paulpf/water-tank-monitor/docs/hardware/20260521_123843.jpg

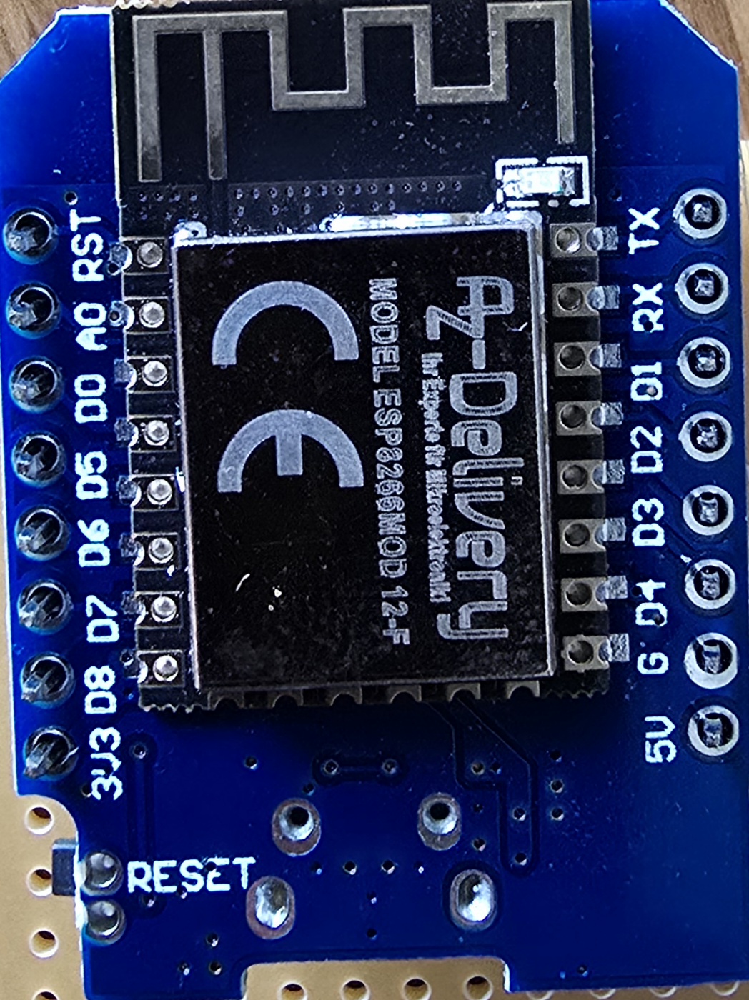
docs/hardware/20260521_123843.jpg
