paulpf/water-tank-monitor/docs/hardware/20260521_123853.jpg

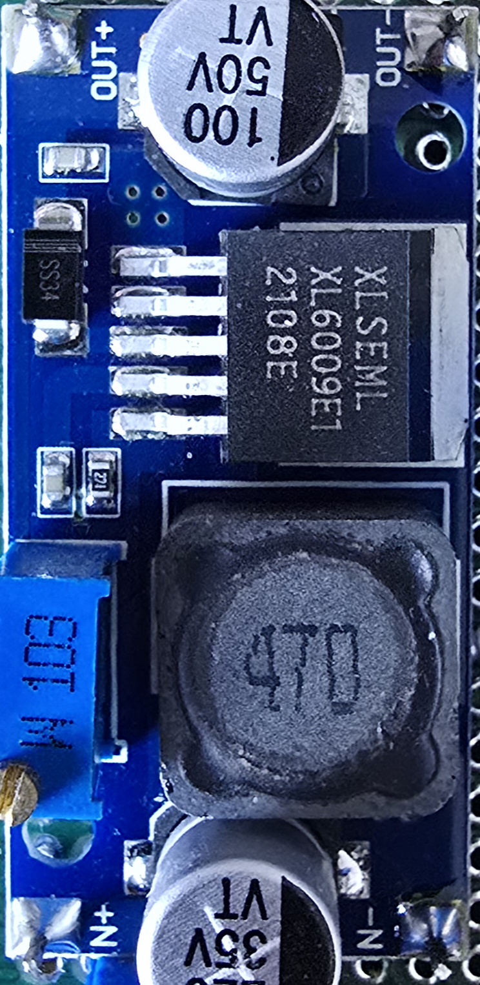
docs/hardware/20260521_123853.jpg
