paulpf/water-tank-monitor/docs/hardware/20260521_123857.jpg

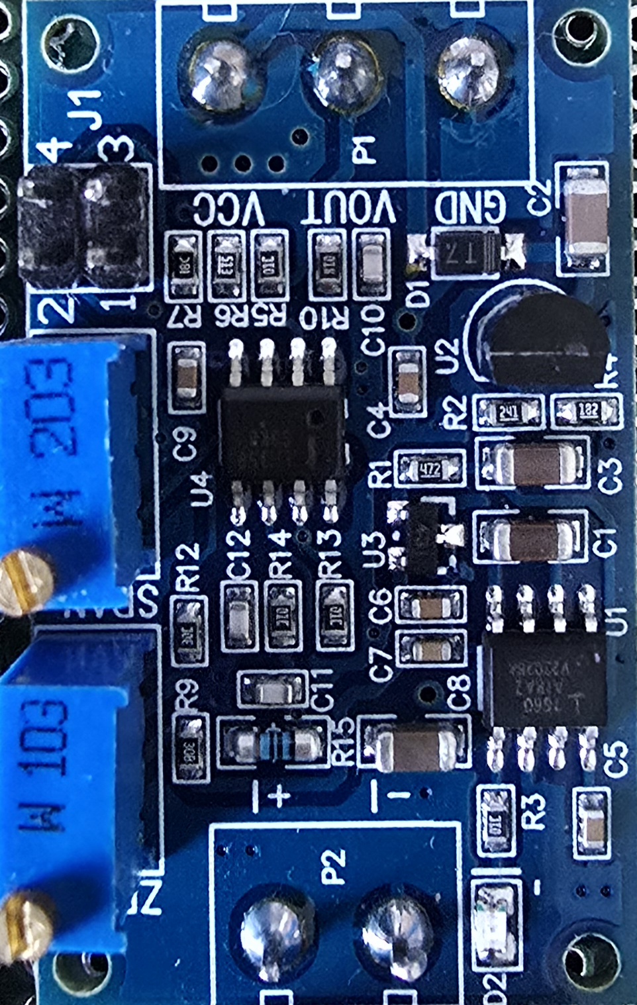
docs/hardware/20260521_123857.jpg
