paulpf/water-tank-monitor/docs/hardware/20260521_123901.jpg

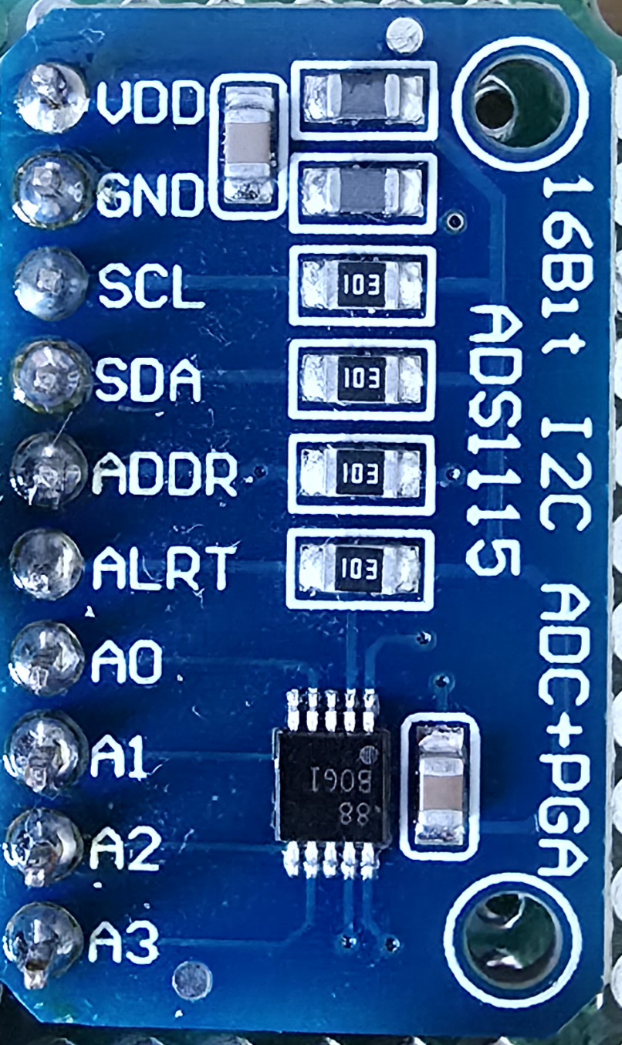
docs/hardware/20260521_123901.jpg
